CedarGroveStudios/CorrosionMonitor/photos and graphics/4752DF75-CB4D-47C5-B14A-65CF91079B80_1_105_c.jpeg

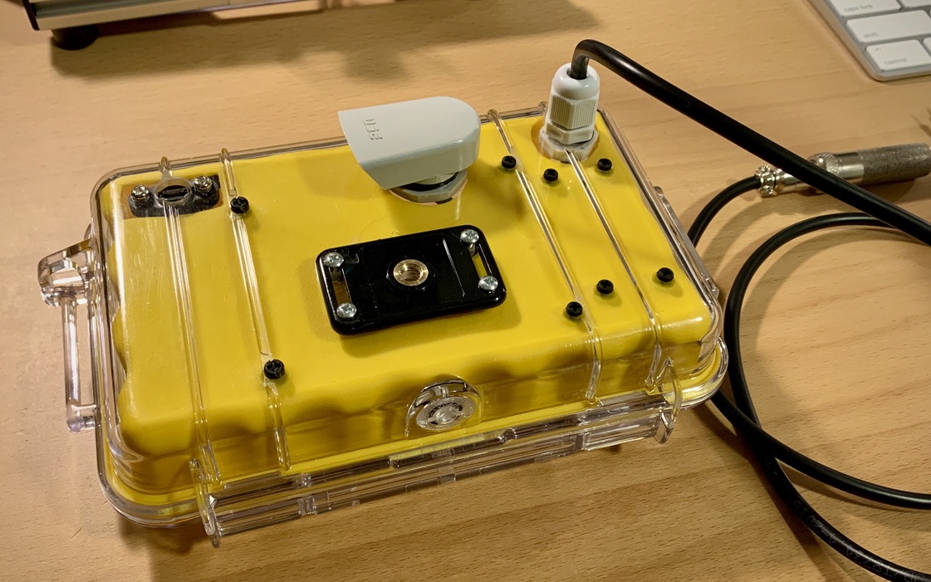
photos and graphics/4752DF75-CB4D-47C5-B14A-65CF91079B80_1_105_c.jpeg
