CedarGroveStudios/CorrosionMonitor/photos and graphics/D7E6778F-555B-4B73-B1ED-6D8061E5138B_1_105_c.jpeg

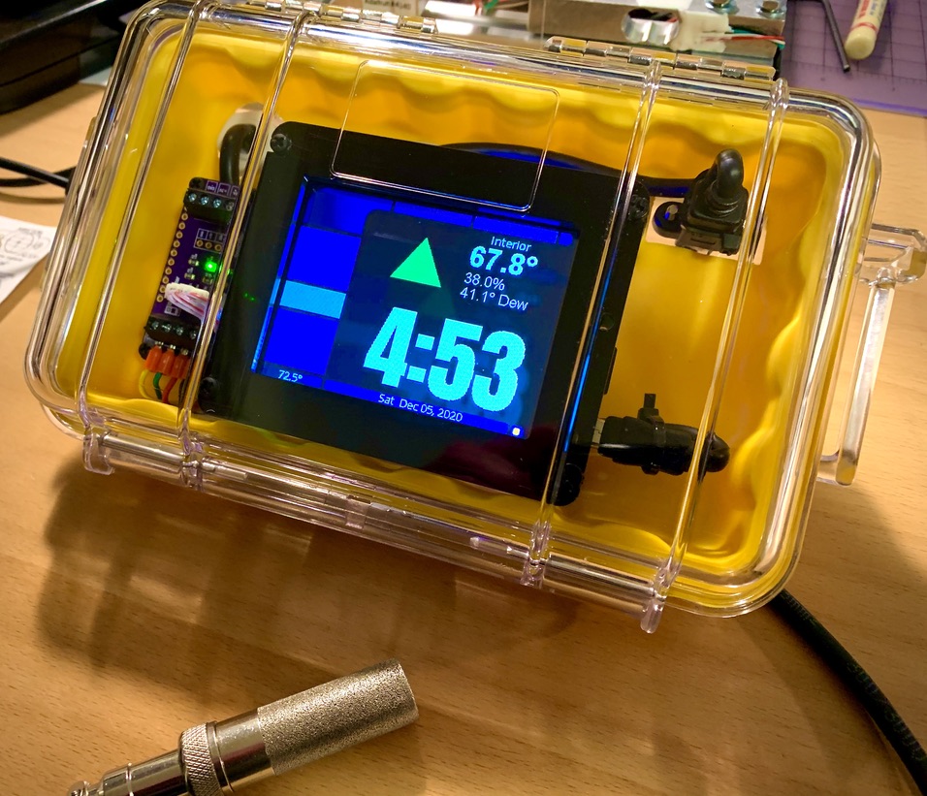
photos and graphics/D7E6778F-555B-4B73-B1ED-6D8061E5138B_1_105_c.jpeg
