CedarGroveStudios/CorrosionMonitor/photos and graphics/DSC06197.JPG

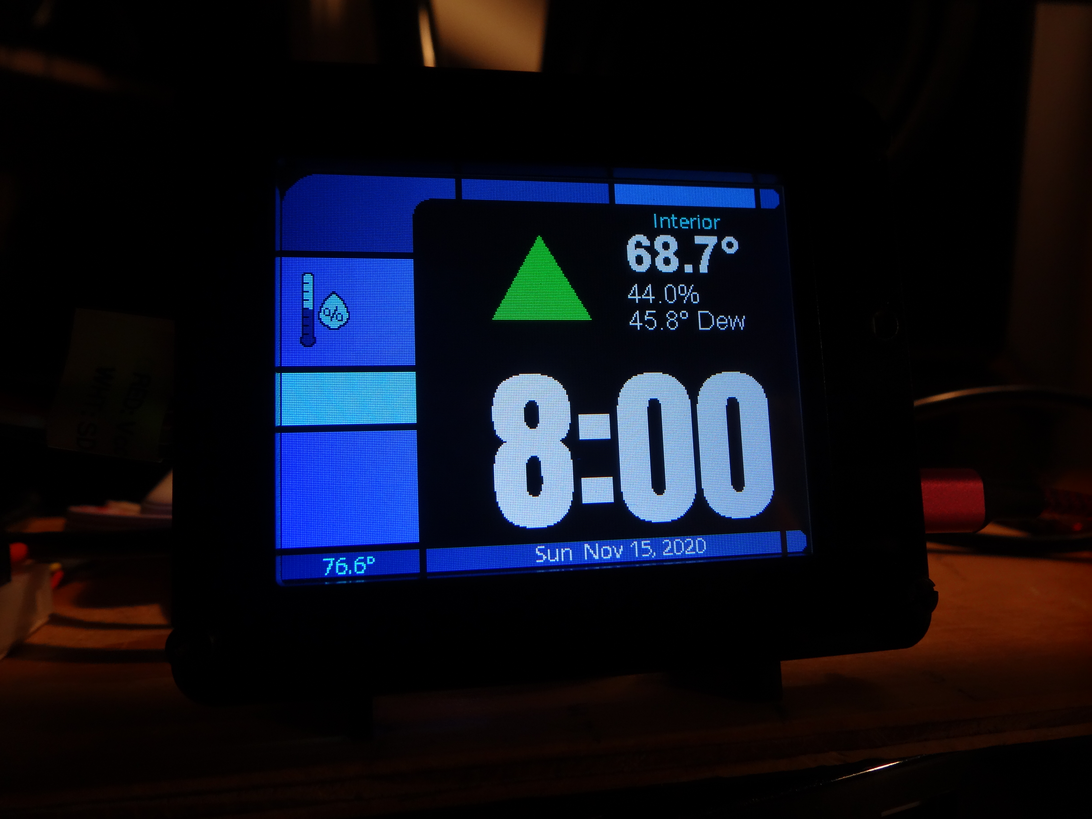
photos and graphics/DSC06197.JPG
