CedarGroveStudios/CorrosionMonitor/photos and graphics/DSC06198.JPG

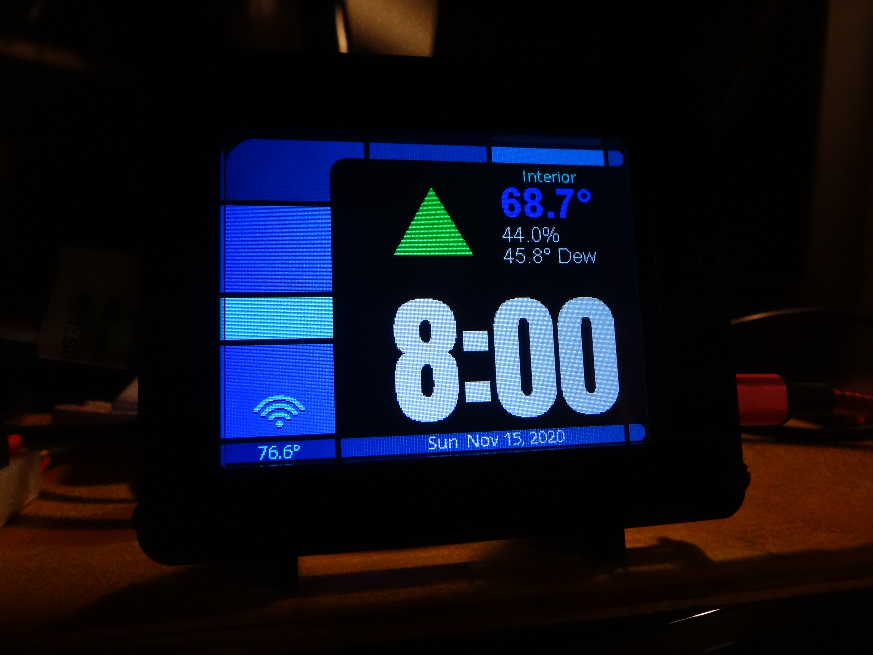
photos and graphics/DSC06198.JPG
