CedarGroveStudios/CorrosionMonitor/photos and graphics/DSC06199.JPG

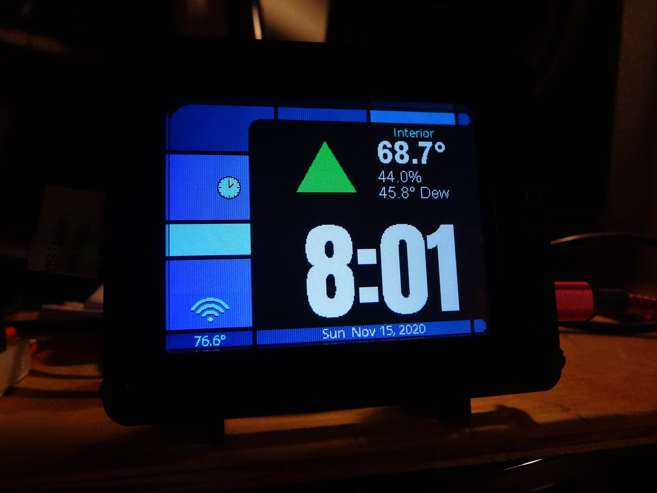
photos and graphics/DSC06199.JPG
