CedarGroveStudios/CorrosionMonitor/photos and graphics/workshop_corrosion_monitor_composite.png

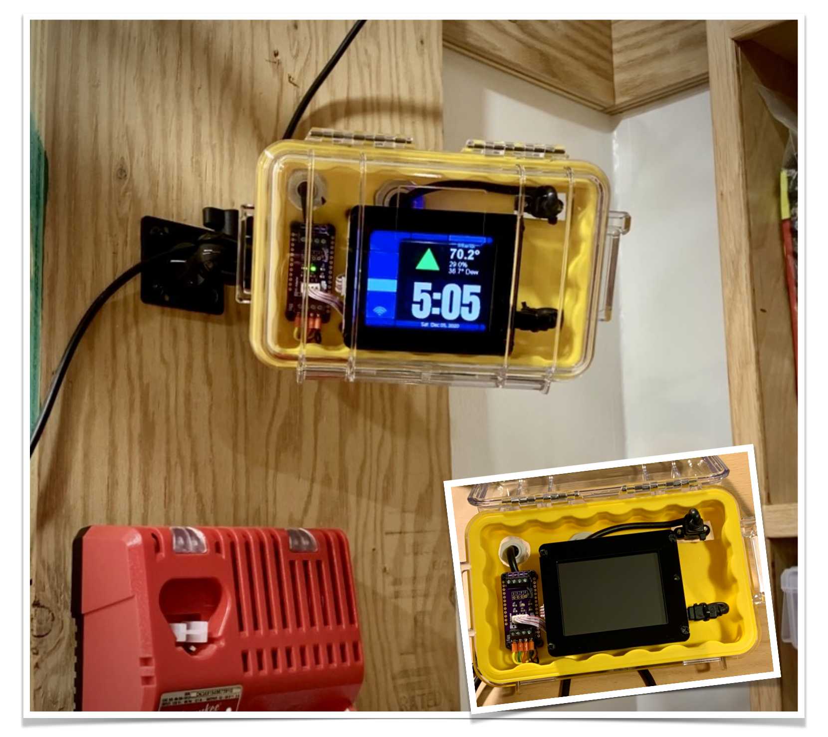
photos and graphics/workshop_corrosion_monitor_composite.png
